FireMarshmellow/ESP32-Cam_With_Thermal-printer/Test scripts/Basic_print_bitmap/mybitmap.h

// Dimensions of your bitmap
const uint16_t my_bitmap_width  = 400;  // replace with your actual width
const uint16_t my_bitmap_height = 400;  // replace with your actual height

// Bitmap data: 1 bit per pixel, row-packed, MSB first. Total bytes = height * ((width+7)/8).
const uint8_t my_bitmap[] PROGMEM = {
// 'IMG_29363', 400x400px
0x55, 0x55, 0x55, 0x57, 0x55, 0x55, 0x55, 0x55, 0x55, 0x57, 0x55, 0x57, 0x55, 0x55, 0x55, 0x55, 
0x55, 0x55, 0x55, 0x55, 0x55, 0x55, 0x55, 0x55, 0x57, 0x55, 0x55, 0x55, 0x55, 0x77, 0x55, 0x55, 
0x55, 0x51, 0x55, 0x55, 0x55, 0xf5, 0x55, 0x51, 0x55, 0x55, 0x55, 0x11, 0x41, 0x55, 0x51, 0x51, 
0x55, 0x11, 0xbb, 0xbb, 0xbb, 0xab, 0xab, 0xab, 0xba, 0xaa, 0xaa, 0xab, 0xbb, 0xaf, 0xff, 0xbb, 
0xfb, 0xbb, 0xbb, 0xbb, 0xbb, 0xbb, 0xbb, 0xbb, 0xbb, 0xba, 0xbf, 0xaa, 0xa0, 0x30, 0x23, 0xfe, 
0x3a, 0x2a, 0x28, 0x23, 0x2a, 0x02, 0x7b, 0xee, 0x32, 0x00, 0x00, 0x32, 0x02, 0x00, 0x20, 0x2a, 
0x03, 0xf8, 0x30, 0x00, 0x55, 0x55, 0x55, 0x55, 0x55, 0x55, 0x55, 0x55, 0x55, 0x55, 0x55, 0x55, 
0xd5, 0x55, 0x55, 0x55, 0x55, 0x55, 0x55, 0x55, 0x55, 0x55, 0x55, 0x55, 0x55, 0x5d, 0x55, 0x55, 
0x55, 0x55, 0x55, 0x5d, 0x55, 0x55, 0x55, 0x55, 0x7d, 0x5f, 0x54, 0x14, 0x45, 0x75, 0x55, 0x45, 
0x11, 0x55, 0x55, 0x54, 0x55, 0x04, 0xaa, 0xaa, 0xae, 0xaa, 0xfb, 0xfa, 0xe0, 0xaa, 0xe8, 0xea, 
0xaa, 0xab, 0xfe, 0xae, 0xff, 0xff, 0xff, 0xaa, 0xaa, 0xaa, 0xaa, 0xaa, 0xaa, 0xae, 0xb8, 0xea, 
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
0x00, 0xa8, 0xaa, 0x0e, 0xa8, 0x08, 0xe0, 0xef, 0x55, 0x55, 0x55, 0x55, 0x75, 0x55, 0x55, 0x55, 
0x55, 0x55, 0x55, 0x55, 0x55, 0x55, 0x55, 0x55, 0x55, 0x55, 0x55, 0x55, 0x55, 0x55, 0x55, 0x57, 
0x55, 0x55, 0x55, 0x55, 0x57, 0x7d, 0x55, 0x55, 0x51, 0x55, 0x55, 0x11, 0x15, 0x55, 0x15, 0x11, 
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
};
